kiteCTRL/kiteTRAK/kiteTRAK/include/bitmaps.h

// Art and assets made and used from https://lopaka.app/

// Drifloon Bitmaps
static const unsigned char PROGMEM drifloon_left_bmp[] = {0x03,0x00,0x0f,0xc0,0x1f,0xe0,0x1f,0xc0,0x3f,0xc0,0x46,0x20,0x40,0x20,0x80,0x10,0xa0,0x10,0x80,0x10,0x41,0x20,0x40,0x20,0x30,0xf0,0x0f,0x18,0x14,0x34,0x26,0x44,0x21,0xc2,0x18,0x02,0x3c,0x02,0x18,0x0c,0x00,0x1e,0x00,0x0c};
static const unsigned char PROGMEM drifloon_right_bmp[] = {0x01,0x80,0x07,0xe0,0x0f,0xf0,0x07,0xf0,0x07,0xf8,0x08,0xc4,0x08,0x04,0x10,0x02,0x10,0x0a,0x10,0x02,0x09,0x04,0x08,0x04,0x1e,0x18,0x31,0xe0,0x58,0x50,0x44,0xc8,0x87,0x08,0x80,0x30,0x80,0x78,0x60,0x30,0xf0,0x00,0x60,0x00};

// Menu Border
static const unsigned char PROGMEM menu_border_bmp[] = {0x07,0xff,0xff,0xff,0xff,0xff,0xff,0xff,0xff,0xff,0xff,0xe0,0x18,0x00,0x00,0x00,0x00,0x00,0x00,0x00,0x00,0x00,0x00,0x18,0x20,0x00,0x00,0x00,0x00,0x00,0x00,0x00,0x00,0x00,0x00,0x0c,0x40,0x00,0x00,0x00,0x00,0x00,0x00,0x00,0x00,0x00,0x00,0x06,0x40,0x00,0x00,0x00,0x00,0x00,0x00,0x00,0x00,0x00,0x00,0x06,0x80,0x00,0x00,0x00,0x00,0x00,0x00,0x00,0x00,0x00,0x00,0x07,0x80,0x00,0x00,0x00,0x00,0x00,0x00,0x00,0x00,0x00,0x00,0x07,0x80,0x00,0x00,0x00,0x00,0x00,0x00,0x00,0x00,0x00,0x00,0x07,0x80,0x00,0x00,0x00,0x00,0x00,0x00,0x00,0x00,0x00,0x00,0x07,0x80,0x00,0x00,0x00,0x00,0x00,0x00,0x00,0x00,0x00,0x00,0x07,0x80,0x00,0x00,0x00,0x00,0x00,0x00,0x00,0x00,0x00,0x00,0x07,0x80,0x00,0x00,0x00,0x00,0x00,0x00,0x00,0x00,0x00,0x00,0x07,0x80,0x00,0x00,0x00,0x00,0x00,0x00,0x00,0x00,0x00,0x00,0x07,0x80,0x00,0x00,0x00,0x00,0x00,0x00,0x00,0x00,0x00,0x00,0x07,0x80,0x00,0x00,0x00,0x00,0x00,0x00,0x00,0x00,0x00,0x00,0x07,0x80,0x00,0x00,0x00,0x00,0x00,0x00,0x00,0x00,0x00,0x00,0x07,0x80,0x00,0x00,0x00,0x00,0x00,0x00,0x00,0x00,0x00,0x00,0x07,0x80,0x00,0x00,0x00,0x00,0x00,0x00,0x00,0x00,0x00,0x00,0x07,0x80,0x00,0x00,0x00,0x00,0x00,0x00,0x00,0x00,0x00,0x00,0x07,0x80,0x00,0x00,0x00,0x00,0x00,0x00,0x00,0x00,0x00,0x00,0x07,0x80,0x00,0x00,0x00,0x00,0x00,0x00,0x00,0x00,0x00,0x00,0x07,0x80,0x00,0x00,0x00,0x00,0x00,0x00,0x00,0x00,0x00,0x00,0x07,0x80,0x00,0x00,0x00,0x00,0x00,0x00,0x00,0x00,0x00,0x00,0x07,0x80,0x00,0x00,0x00,0x00,0x00,0x00,0x00,0x00,0x00,0x00,0x07,0x80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
