kiteCTRL/kiteTRAK/rp2040/extras/extras.h

#ifndef EXTRAS_H
#define EXTRAS_H

/* Plugins and extra features outside the normal scope of
 * the PhobGCC can be found here. Uncomment each #define
 * to include the features they provide in a build then
 * set the configuration slot it uses (if it needs configuration)
 *
 */
//------------------------------------------------------
//#define EXTRAS_ESS
#define EXTRAS_KT
//------------------------------------------------------

#ifdef EXTRAS_ESS
#include "ess.h"
#endif

#ifdef EXTRAS_KT
#include "kt.h"
#endif

typedef bool(*ExtrasToggleFn)(IntOrFloat config[]);//Used for toggling extras
typedef void(*ExtrasConfigFn)(IntOrFloat config[], Cardinals dpad);//Used for configuring extras with the Dpad

struct ExtrasFunctions{
	ExtrasToggleFn toggleFn;
	ExtrasConfigFn configFn;
};

static ExtrasFunctions extrasFunctions[EXTRAS_SIZE] = {NULL};

void extrasConfigAssign(ExtrasSlot slot, ExtrasToggleFn toggleFn, ExtrasConfigFn configFn){
	switch(slot){
		case EXTRAS_UP:
			debug_println("Extra: Setting configuration to Up...");
			break;
		case EXTRAS_DOWN:
			debug_println("Extra: Setting configuration to Down...");
			break;
		case EXTRAS_LEFT:
			debug_println("Extra: Setting configuration to Left...");
			break;
		case EXTRAS_RIGHT:
			debug_println("Extra: Setting configuration to Right...");
			break;
		case EXTRAS_UNSET:
			debug_println("Extra: Configuration slot not set, feature will be inaccessible.");
			return;
		default:
			debug_println("Extra: Invalid configuration slot requested, feature will be inaccessible.");
			return;
	}
	ExtrasFunctions &fns = extrasFunctions[slot];
	if(fns.toggleFn || fns.configFn) {
		debug_println("Extra: Warning! Configuration slot was already in use, previous feature will be inaccessible.");
	}
	fns.toggleFn = toggleFn;
	fns.configFn = configFn;
}

void extrasInit() {
	/*----------------------------------------------------------
	 * Configuration slots for extras, the available options are:
	 *	- EXTRAS_UP
	 *	- EXTRAS_DOWN
	 *	- EXTRAS_LEFT
	 *	- EXTRAS_RIGHT
	 * Make sure to set the slot from EXTRAS_UNSET to one of the
	 * above for the extras below if applicable!
	 */
#ifdef EXTRAS_ESS
	//-----------------------------------------
	ess::extrasEssConfigSlot = EXTRAS_UNSET;
	//-----------------------------------------
	debug_println("Extra: Enabling ESS functionality...");
	extrasConfigAssign(ess::extrasEssConfigSlot, ess::toggle, NULL);
#endif

#ifdef EXTRAS_KT
	//-----------------------------------------
	kt::extrasKtConfigSlot = EXTRAS_UP;
	//-----------------------------------------
	debug_println("Extra: Enabling KT functionality...");
	extrasConfigAssign(kt::extrasKtConfigSlot, kt::toggle, NULL);
#endif

}

#endif //EXTRAS_H
